OPEnSLab-OSU/Dendrometer/AS5311_Prototype/AS5331_Integration/AS5331.h

// Returns the serial output from AS5331
uint32_t bitbang(int CLK, int CS, int DO) {
  // write clock high to select the angular position data
  digitalWrite(CLK, HIGH);
  delay(1);
  // select the chip
  digitalWrite(CS, LOW);
  delay(1);
  digitalWrite(CLK, LOW);
  // read the value in it's entirety
  uint32_t value = 0;
  for (uint8_t i = 0; i < 18; i++) {
    delay(1);
    digitalWrite(CLK, HIGH);
    delay(1);
    digitalWrite(CLK, LOW);
    delay(1);
    auto readval = digitalRead(DO);
    if (readval == HIGH)
      value |= (1U << i);
  }
  digitalWrite(CS, HIGH);
  return value;
}

// Isolates the bottom 12 bits position value to decimal
uint32_t convertBits(uint32_t num) {
      uint32_t readval = num & 0xFFF;
      uint32_t newval = 0;
    // Flips bits order
      for (int i = 11; i >= 0; i--) 
      {
        uint32_t exists = (readval & (1 << i)) ? 1 : 0;
        newval |= (exists << (11 - i));
      }
      return newval;

}
